imbiribajr/MEU_CONSOLE_FPGA_DE0_SD/fotos/IMG_20260413_175017.jpg

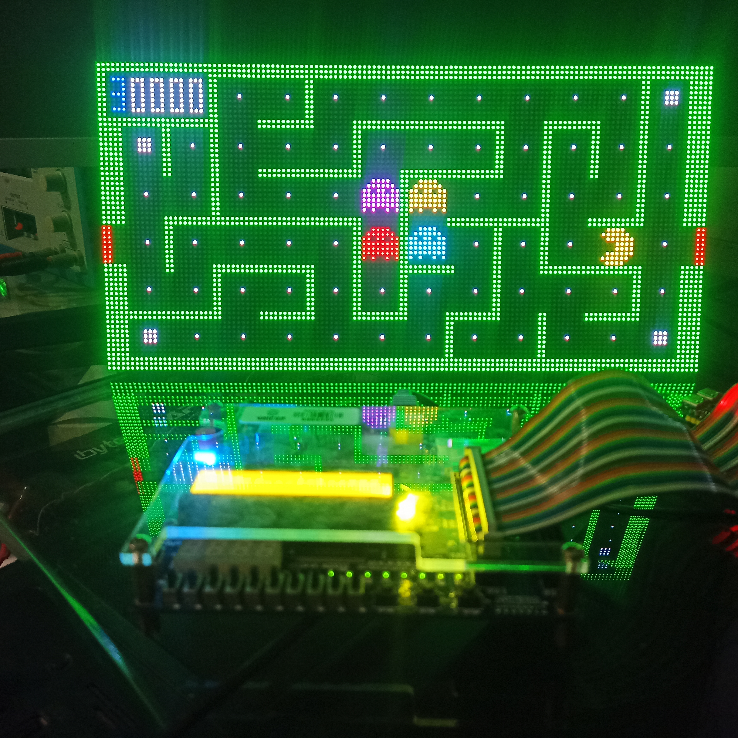
fotos/IMG_20260413_175017.jpg
