imbiribajr/MEU_CONSOLE_FPGA_DE0_SD/fotos/WhatsApp Image 2026-05-14 at 15.44.31 (2).jpeg

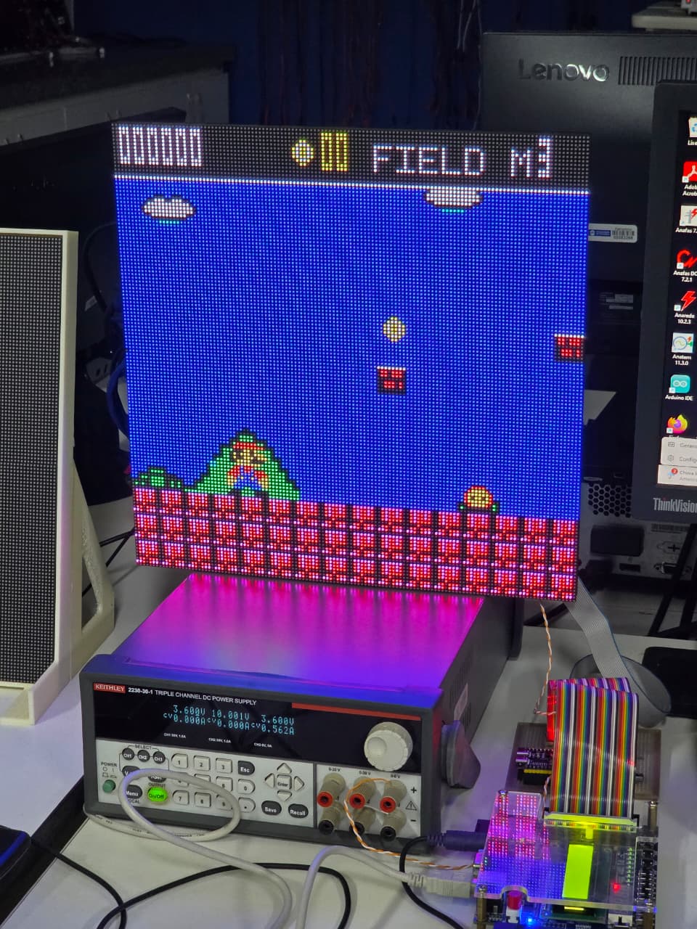
fotos/WhatsApp Image 2026-05-14 at 15.44.31 (2).jpeg
