imbiribajr/MEU_CONSOLE_FPGA_DE0_SD/hardware/NiosII_ps2/synthesis/niosii_ps2_rst_controller.vhd

-- niosii_ps2_rst_controller.vhd

-- Generated using ACDS version 13.0sp1 232 at 2026.03.27.22:52:36

library IEEE;
use IEEE.std_logic_1164.all;
use IEEE.numeric_std.all;

entity niosii_ps2_rst_controller is
	generic (
		NUM_RESET_INPUTS        : integer := 3;
		OUTPUT_RESET_SYNC_EDGES : string  := "deassert";
		SYNC_DEPTH              : integer := 2;
		RESET_REQUEST_PRESENT   : integer := 1
	);
	port (
		reset_in0  : in  std_logic := '0'; -- reset_in0.reset
		reset_in1  : in  std_logic := '0'; -- reset_in1.reset
		reset_in2  : in  std_logic := '0'; -- reset_in2.reset
		clk        : in  std_logic := '0'; --       clk.clk
		reset_out  : out std_logic;        -- reset_out.reset
		reset_req  : out std_logic;        --          .reset_req
		reset_in10 : in  std_logic := '0';
		reset_in11 : in  std_logic := '0';
		reset_in12 : in  std_logic := '0';
		reset_in13 : in  std_logic := '0';
		reset_in14 : in  std_logic := '0';
		reset_in15 : in  std_logic := '0';
		reset_in3  : in  std_logic := '0';
		reset_in4  : in  std_logic := '0';
		reset_in5  : in  std_logic := '0';
		reset_in6  : in  std_logic := '0';
		reset_in7  : in  std_logic := '0';
		reset_in8  : in  std_logic := '0';
		reset_in9  : in  std_logic := '0'
	);
end entity niosii_ps2_rst_controller;

architecture rtl of niosii_ps2_rst_controller is
	component altera_reset_controller is
		generic (
			NUM_RESET_INPUTS        : integer := 6;
			OUTPUT_RESET_SYNC_EDGES : string  := "deassert";
			SYNC_DEPTH              : integer := 2;
			RESET_REQUEST_PRESENT   : integer := 0
		);
		port (
			reset_in0  : in  std_logic := 'X'; -- reset
			reset_in1  : in  std_logic := 'X'; -- reset
			reset_in2  : in  std_logic := 'X'; -- reset
			clk        : in  std_logic := 'X'; -- clk
			reset_out  : out std_logic;        -- reset
			reset_req  : out std_logic;        -- reset_req
			reset_in3  : in  std_logic := 'X'; -- reset
			reset_in4  : in  std_logic := 'X'; -- reset
			reset_in5  : in  std_logic := 'X'; -- reset
			reset_in6  : in  std_logic := 'X'; -- reset
			reset_in7  : in  std_logic := 'X'; -- reset
			reset_in8  : in  std_logic := 'X'; -- reset
			reset_in9  : in  std_logic := 'X'; -- reset
			reset_in10 : in  std_logic := 'X'; -- reset
			reset_in11 : in  std_logic := 'X'; -- reset
			reset_in12 : in  std_logic := 'X'; -- reset
			reset_in13 : in  std_logic := 'X'; -- reset
			reset_in14 : in  std_logic := 'X'; -- reset
			reset_in15 : in  std_logic := 'X'  -- reset
		);
	end component altera_reset_controller;

begin

	rst_controller : component altera_reset_controller
		generic map (
			NUM_RESET_INPUTS        => NUM_RESET_INPUTS,
			OUTPUT_RESET_SYNC_EDGES => OUTPUT_RESET_SYNC_EDGES,
			SYNC_DEPTH              => SYNC_DEPTH,
			RESET_REQUEST_PRESENT   => RESET_REQUEST_PRESENT
		)
		port map (
			reset_in0  => reset_in0, -- reset_in0.reset
			reset_in1  => reset_in1, -- reset_in1.reset
			reset_in2  => reset_in2, -- reset_in2.reset
			clk        => clk,       --       clk.clk
			reset_out  => reset_out, -- reset_out.reset
			reset_req  => reset_req, --          .reset_req
			reset_in3  => '0',       -- (terminated)
			reset_in4  => '0',       -- (terminated)
			reset_in5  => '0',       -- (terminated)
			reset_in6  => '0',       -- (terminated)
			reset_in7  => '0',       -- (terminated)
			reset_in8  => '0',       -- (terminated)
			reset_in9  => '0',       -- (terminated)
			reset_in10 => '0',       -- (terminated)
			reset_in11 => '0',       -- (terminated)
			reset_in12 => '0',       -- (terminated)
			reset_in13 => '0',       -- (terminated)
			reset_in14 => '0',       -- (terminated)
			reset_in15 => '0'        -- (terminated)
		);

end architecture rtl; -- of niosii_ps2_rst_controller
