imbiribajr/MEU_CONSOLE_FPGA_DE0_SD/software/bsp/system.h

/*
 * system.h - SOPC Builder system and BSP software package information
 *
 * Machine generated for CPU 'nios2_qsys_0' in SOPC Builder design 'NiosII_ps2'
 * SOPC Builder design path: F:/Jogos_FPGA/MEU_CONSOLE_FPGA_DE0_SD/hardware/niosII_ps2.sopcinfo
 *
 * Generated: Mon Apr 13 18:09:35 BRT 2026
 */

/*
 * DO NOT MODIFY THIS FILE
 *
 * Changing this file will have subtle consequences
 * which will almost certainly lead to a nonfunctioning
 * system. If you do modify this file, be aware that your
 * changes will be overwritten and lost when this file
 * is generated again.
 *
 * DO NOT MODIFY THIS FILE
 */

/*
 * License Agreement
 *
 * Copyright (c) 2008
 * Altera Corporation, San Jose, California, USA.
 * All rights reserved.
 *
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
 * This agreement shall be governed in all respects by the laws of the State
 * of California and by the laws of the United States of America.
 */

#ifndef __SYSTEM_H_
#define __SYSTEM_H_

/* Include definitions from linker script generator */
#include "linker.h"


/*
 * CPU configuration
 *
 */

#define ALT_CPU_ARCHITECTURE "altera_nios2_qsys"
#define ALT_CPU_BIG_ENDIAN 0
#define ALT_CPU_BREAK_ADDR 0x1810820
#define ALT_CPU_CPU_FREQ 50000000u
#define ALT_CPU_CPU_ID_SIZE 1
#define ALT_CPU_CPU_ID_VALUE 0x00000000
#define ALT_CPU_CPU_IMPLEMENTATION "fast"
#define ALT_CPU_DATA_ADDR_WIDTH 0x19
#define ALT_CPU_DCACHE_LINE_SIZE 32
#define ALT_CPU_DCACHE_LINE_SIZE_LOG2 5
#define ALT_CPU_DCACHE_SIZE 2048
#define ALT_CPU_EXCEPTION_ADDR 0x180c020
#define ALT_CPU_FLUSHDA_SUPPORTED
#define ALT_CPU_FREQ 50000000
#define ALT_CPU_HARDWARE_DIVIDE_PRESENT 1
#define ALT_CPU_HARDWARE_MULTIPLY_PRESENT 1
#define ALT_CPU_HARDWARE_MULX_PRESENT 0
#define ALT_CPU_HAS_DEBUG_CORE 1
#define ALT_CPU_HAS_DEBUG_STUB
#define ALT_CPU_HAS_JMPI_INSTRUCTION
#define ALT_CPU_ICACHE_LINE_SIZE 32
#define ALT_CPU_ICACHE_LINE_SIZE_LOG2 5
#define ALT_CPU_ICACHE_SIZE 4096
#define ALT_CPU_INITDA_SUPPORTED
#define ALT_CPU_INST_ADDR_WIDTH 0x19
#define ALT_CPU_NAME "nios2_qsys_0"
#define ALT_CPU_NUM_OF_SHADOW_REG_SETS 0
#define ALT_CPU_RESET_ADDR 0x180c000


/*
 * CPU configuration (with legacy prefix - don't use these anymore)
 *
 */

#define NIOS2_BIG_ENDIAN 0
#define NIOS2_BREAK_ADDR 0x1810820
#define NIOS2_CPU_FREQ 50000000u
#define NIOS2_CPU_ID_SIZE 1
#define NIOS2_CPU_ID_VALUE 0x00000000
#define NIOS2_CPU_IMPLEMENTATION "fast"
#define NIOS2_DATA_ADDR_WIDTH 0x19
#define NIOS2_DCACHE_LINE_SIZE 32
#define NIOS2_DCACHE_LINE_SIZE_LOG2 5
#define NIOS2_DCACHE_SIZE 2048
#define NIOS2_EXCEPTION_ADDR 0x180c020
#define NIOS2_FLUSHDA_SUPPORTED
#define NIOS2_HARDWARE_DIVIDE_PRESENT 1
#define NIOS2_HARDWARE_MULTIPLY_PRESENT 1
#define NIOS2_HARDWARE_MULX_PRESENT 0
#define NIOS2_HAS_DEBUG_CORE 1
#define NIOS2_HAS_DEBUG_STUB
#define NIOS2_HAS_JMPI_INSTRUCTION
#define NIOS2_ICACHE_LINE_SIZE 32
#define NIOS2_ICACHE_LINE_SIZE_LOG2 5
#define NIOS2_ICACHE_SIZE 4096
#define NIOS2_INITDA_SUPPORTED
#define NIOS2_INST_ADDR_WIDTH 0x19
#define NIOS2_NUM_OF_SHADOW_REG_SETS 0
#define NIOS2_RESET_ADDR 0x180c000


/*
 * Define for each module class mastered by the CPU
 *
 */

#define __ALTERA_AVALON_JTAG_UART
#define __ALTERA_AVALON_NEW_SDRAM_CONTROLLER
#define __ALTERA_AVALON_ONCHIP_MEMORY2
#define __ALTERA_AVALON_PIO
#define __ALTERA_AVALON_SPI
#define __ALTERA_AVALON_SYSID_QSYS
#define __ALTERA_AVALON_UART
#define __ALTERA_GENERIC_TRISTATE_CONTROLLER
#define __ALTERA_NIOS2_QSYS
#define __LED_MATRIX_AVALON
#define __PS2_INTERFACE


/*
 * System configuration
 *
 */

#define ALT_DEVICE_FAMILY "Cyclone III"
#define ALT_ENHANCED_INTERRUPT_API_PRESENT
#define ALT_IRQ_BASE NULL
#define ALT_LOG_PORT "/dev/null"
#define ALT_LOG_PORT_BASE 0x0
#define ALT_LOG_PORT_DEV null
#define ALT_LOG_PORT_TYPE ""
#define ALT_NUM_EXTERNAL_INTERRUPT_CONTROLLERS 0
#define ALT_NUM_INTERNAL_INTERRUPT_CONTROLLERS 1
#define ALT_NUM_INTERRUPT_CONTROLLERS 1
#define ALT_STDERR "/dev/jtag_uart_0"
#define ALT_STDERR_BASE 0x18110b8
#define ALT_STDERR_DEV jtag_uart_0
#define ALT_STDERR_IS_JTAG_UART
#define ALT_STDERR_PRESENT
#define ALT_STDERR_TYPE "altera_avalon_jtag_uart"
#define ALT_STDIN "/dev/jtag_uart_0"
#define ALT_STDIN_BASE 0x18110b8
#define ALT_STDIN_DEV jtag_uart_0
#define ALT_STDIN_IS_JTAG_UART
#define ALT_STDIN_PRESENT
#define ALT_STDIN_TYPE "altera_avalon_jtag_uart"
#define ALT_STDOUT "/dev/jtag_uart_0"
#define ALT_STDOUT_BASE 0x18110b8
#define ALT_STDOUT_DEV jtag_uart_0
#define ALT_STDOUT_IS_JTAG_UART
#define ALT_STDOUT_PRESENT
#define ALT_STDOUT_TYPE "altera_avalon_jtag_uart"
#define ALT_SYSTEM_NAME "NiosII_ps2"


/*
 * generic_tristate_controller_0 configuration
 *
 */

#define ALT_MODULE_CLASS_generic_tristate_controller_0 altera_generic_tristate_controller
#define GENERIC_TRISTATE_CONTROLLER_0_BASE 0x1400000
#define GENERIC_TRISTATE_CONTROLLER_0_HOLD_VALUE 0
#define GENERIC_TRISTATE_CONTROLLER_0_IRQ -1
#define GENERIC_TRISTATE_CONTROLLER_0_IRQ_INTERRUPT_CONTROLLER_ID -1
#define GENERIC_TRISTATE_CONTROLLER_0_NAME "/dev/generic_tristate_controller_0"
#define GENERIC_TRISTATE_CONTROLLER_0_SETUP_VALUE 0
#define GENERIC_TRISTATE_CONTROLLER_0_SIZE 262144u
#define GENERIC_TRISTATE_CONTROLLER_0_SPAN 4194304
#define GENERIC_TRISTATE_CONTROLLER_0_TIMING_UNITS "ns"
#define GENERIC_TRISTATE_CONTROLLER_0_TYPE "altera_generic_tristate_controller"
#define GENERIC_TRISTATE_CONTROLLER_0_WAIT_VALUE 0


/*
 * hal configuration
 *
 */

#define ALT_MAX_FD 4
#define ALT_SYS_CLK none
#define ALT_TIMESTAMP_CLK none


/*
 * i2c_clk configuration
 *
 */

#define ALT_MODULE_CLASS_i2c_clk altera_avalon_pio
#define I2C_CLK_BASE 0x1811080
#define I2C_CLK_BIT_CLEARING_EDGE_REGISTER 0
#define I2C_CLK_BIT_MODIFYING_OUTPUT_REGISTER 0
#define I2C_CLK_CAPTURE 0
#define I2C_CLK_DATA_WIDTH 1
#define I2C_CLK_DO_TEST_BENCH_WIRING 0
#define I2C_CLK_DRIVEN_SIM_VALUE 0
#define I2C_CLK_EDGE_TYPE "NONE"
#define I2C_CLK_FREQ 50000000
#define I2C_CLK_HAS_IN 0
#define I2C_CLK_HAS_OUT 1
#define I2C_CLK_HAS_TRI 0
#define I2C_CLK_IRQ -1
#define I2C_CLK_IRQ_INTERRUPT_CONTROLLER_ID -1
#define I2C_CLK_IRQ_TYPE "NONE"
#define I2C_CLK_NAME "/dev/i2c_clk"
#define I2C_CLK_RESET_VALUE 0
#define I2C_CLK_SPAN 16
#define I2C_CLK_TYPE "altera_avalon_pio"


/*
 * i2c_sda configuration
 *
 */

#define ALT_MODULE_CLASS_i2c_sda altera_avalon_pio
#define I2C_SDA_BASE 0x1811070
#define I2C_SDA_BIT_CLEARING_EDGE_REGISTER 0
#define I2C_SDA_BIT_MODIFYING_OUTPUT_REGISTER 0
#define I2C_SDA_CAPTURE 0
#define I2C_SDA_DATA_WIDTH 1
#define I2C_SDA_DO_TEST_BENCH_WIRING 0
#define I2C_SDA_DRIVEN_SIM_VALUE 0
#define I2C_SDA_EDGE_TYPE "NONE"
#define I2C_SDA_FREQ 50000000
#define I2C_SDA_HAS_IN 0
#define I2C_SDA_HAS_OUT 0
#define I2C_SDA_HAS_TRI 1
#define I2C_SDA_IRQ -1
#define I2C_SDA_IRQ_INTERRUPT_CONTROLLER_ID -1
#define I2C_SDA_IRQ_TYPE "NONE"
#define I2C_SDA_NAME "/dev/i2c_sda"
#define I2C_SDA_RESET_VALUE 0
#define I2C_SDA_SPAN 16
#define I2C_SDA_TYPE "altera_avalon_pio"


/*
 * jtag_uart_0 configuration
 *
 */

#define ALT_MODULE_CLASS_jtag_uart_0 altera_avalon_jtag_uart
#define JTAG_UART_0_BASE 0x18110b8
#define JTAG_UART_0_IRQ 0
#define JTAG_UART_0_IRQ_INTERRUPT_CONTROLLER_ID 0
#define JTAG_UART_0_NAME "/dev/jtag_uart_0"
#define JTAG_UART_0_READ_DEPTH 64
#define JTAG_UART_0_READ_THRESHOLD 8
#define JTAG_UART_0_SPAN 8
#define JTAG_UART_0_TYPE "altera_avalon_jtag_uart"
#define JTAG_UART_0_WRITE_DEPTH 64
#define JTAG_UART_0_WRITE_THRESHOLD 8


/*
 * led_matrix_avalon_0 configuration
 *
 */

#define ALT_MODULE_CLASS_led_matrix_avalon_0 led_matrix_avalon
#define LED_MATRIX_AVALON_0_BASE 0x1808000
#define LED_MATRIX_AVALON_0_IRQ -1
#define LED_MATRIX_AVALON_0_IRQ_INTERRUPT_CONTROLLER_ID -1
#define LED_MATRIX_AVALON_0_NAME "/dev/led_matrix_avalon_0"
#define LED_MATRIX_AVALON_0_SPAN 16384
#define LED_MATRIX_AVALON_0_TYPE "led_matrix_avalon"


/*
 * new_sdram_controller_0 configuration
 *
 */

#define ALT_MODULE_CLASS_new_sdram_controller_0 altera_avalon_new_sdram_controller
#define NEW_SDRAM_CONTROLLER_0_BASE 0x800000
#define NEW_SDRAM_CONTROLLER_0_CAS_LATENCY 3
#define NEW_SDRAM_CONTROLLER_0_CONTENTS_INFO
#define NEW_SDRAM_CONTROLLER_0_INIT_NOP_DELAY 0.0
#define NEW_SDRAM_CONTROLLER_0_INIT_REFRESH_COMMANDS 2
#define NEW_SDRAM_CONTROLLER_0_IRQ -1
#define NEW_SDRAM_CONTROLLER_0_IRQ_INTERRUPT_CONTROLLER_ID -1
#define NEW_SDRAM_CONTROLLER_0_IS_INITIALIZED 1
#define NEW_SDRAM_CONTROLLER_0_NAME "/dev/new_sdram_controller_0"
#define NEW_SDRAM_CONTROLLER_0_POWERUP_DELAY 100.0
#define NEW_SDRAM_CONTROLLER_0_REFRESH_PERIOD 7.8125
#define NEW_SDRAM_CONTROLLER_0_REGISTER_DATA_IN 1
#define NEW_SDRAM_CONTROLLER_0_SDRAM_ADDR_WIDTH 0x16
#define NEW_SDRAM_CONTROLLER_0_SDRAM_BANK_WIDTH 2
#define NEW_SDRAM_CONTROLLER_0_SDRAM_COL_WIDTH 8
#define NEW_SDRAM_CONTROLLER_0_SDRAM_DATA_WIDTH 16
#define NEW_SDRAM_CONTROLLER_0_SDRAM_NUM_BANKS 4
#define NEW_SDRAM_CONTROLLER_0_SDRAM_NUM_CHIPSELECTS 1
#define NEW_SDRAM_CONTROLLER_0_SDRAM_ROW_WIDTH 12
#define NEW_SDRAM_CONTROLLER_0_SHARED_DATA 0
#define NEW_SDRAM_CONTROLLER_0_SIM_MODEL_BASE 0
#define NEW_SDRAM_CONTROLLER_0_SPAN 8388608
#define NEW_SDRAM_CONTROLLER_0_STARVATION_INDICATOR 0
#define NEW_SDRAM_CONTROLLER_0_TRISTATE_BRIDGE_SLAVE ""
#define NEW_SDRAM_CONTROLLER_0_TYPE "altera_avalon_new_sdram_controller"
#define NEW_SDRAM_CONTROLLER_0_T_AC 5.5
#define NEW_SDRAM_CONTROLLER_0_T_MRD 3
#define NEW_SDRAM_CONTROLLER_0_T_RCD 20.0
#define NEW_SDRAM_CONTROLLER_0_T_RFC 70.0
#define NEW_SDRAM_CONTROLLER_0_T_RP 20.0
#define NEW_SDRAM_CONTROLLER_0_T_WR 14.0


/*
 * onchip_memory2_0 configuration
 *
 */

#define ALT_MODULE_CLASS_onchip_memory2_0 altera_avalon_onchip_memory2
#define ONCHIP_MEMORY2_0_ALLOW_IN_SYSTEM_MEMORY_CONTENT_EDITOR 0
#define ONCHIP_MEMORY2_0_ALLOW_MRAM_SIM_CONTENTS_ONLY_FILE 0
#define ONCHIP_MEMORY2_0_BASE 0x180c000
#define ONCHIP_MEMORY2_0_CONTENTS_INFO ""
#define ONCHIP_MEMORY2_0_DUAL_PORT 0
#define ONCHIP_MEMORY2_0_GUI_RAM_BLOCK_TYPE "AUTO"
#define ONCHIP_MEMORY2_0_INIT_CONTENTS_FILE "NiosII_ps2_onchip_memory2_0"
#define ONCHIP_MEMORY2_0_INIT_MEM_CONTENT 1
#define ONCHIP_MEMORY2_0_INSTANCE_ID "NONE"
#define ONCHIP_MEMORY2_0_IRQ -1
#define ONCHIP_MEMORY2_0_IRQ_INTERRUPT_CONTROLLER_ID -1
#define ONCHIP_MEMORY2_0_NAME "/dev/onchip_memory2_0"
#define ONCHIP_MEMORY2_0_NON_DEFAULT_INIT_FILE_ENABLED 0
#define ONCHIP_MEMORY2_0_RAM_BLOCK_TYPE "AUTO"
#define ONCHIP_MEMORY2_0_READ_DURING_WRITE_MODE "DONT_CARE"
#define ONCHIP_MEMORY2_0_SINGLE_CLOCK_OP 0
#define ONCHIP_MEMORY2_0_SIZE_MULTIPLE 1
#define ONCHIP_MEMORY2_0_SIZE_VALUE 16384
#define ONCHIP_MEMORY2_0_SPAN 16384
#define ONCHIP_MEMORY2_0_TYPE "altera_avalon_onchip_memory2"
#define ONCHIP_MEMORY2_0_WRITABLE 1


/*
 * pio_0 configuration
 *
 */

#define ALT_MODULE_CLASS_pio_0 altera_avalon_pio
#define PIO_0_BASE 0x1811090
#define PIO_0_BIT_CLEARING_EDGE_REGISTER 0
#define PIO_0_BIT_MODIFYING_OUTPUT_REGISTER 0
#define PIO_0_CAPTURE 0
#define PIO_0_DATA_WIDTH 4
#define PIO_0_DO_TEST_BENCH_WIRING 0
#define PIO_0_DRIVEN_SIM_VALUE 0
#define PIO_0_EDGE_TYPE "NONE"
#define PIO_0_FREQ 50000000
#define PIO_0_HAS_IN 1
#define PIO_0_HAS_OUT 0
#define PIO_0_HAS_TRI 0
#define PIO_0_IRQ -1
#define PIO_0_IRQ_INTERRUPT_CONTROLLER_ID -1
#define PIO_0_IRQ_TYPE "NONE"
#define PIO_0_NAME "/dev/pio_0"
#define PIO_0_RESET_VALUE 0
#define PIO_0_SPAN 16
#define PIO_0_TYPE "altera_avalon_pio"


/*
 * ps2_interface_0 configuration
 *
 */

#define ALT_MODULE_CLASS_ps2_interface_0 ps2_interface
#define PS2_INTERFACE_0_BASE 0x18110c4
#define PS2_INTERFACE_0_IRQ -1
#define PS2_INTERFACE_0_IRQ_INTERRUPT_CONTROLLER_ID -1
#define PS2_INTERFACE_0_NAME "/dev/ps2_interface_0"
#define PS2_INTERFACE_0_SPAN 4
#define PS2_INTERFACE_0_TYPE "ps2_interface"


/*
 * sd_spi_0 configuration
 *
 */

#define ALT_MODULE_CLASS_sd_spi_0 altera_avalon_spi
#define SD_SPI_0_BASE 0x1811000
#define SD_SPI_0_CLOCKMULT 1
#define SD_SPI_0_CLOCKPHASE 0
#define SD_SPI_0_CLOCKPOLARITY 0
#define SD_SPI_0_CLOCKUNITS "Hz"
#define SD_SPI_0_DATABITS 8
#define SD_SPI_0_DATAWIDTH 16
#define SD_SPI_0_DELAYMULT "1.0E-9"
#define SD_SPI_0_DELAYUNITS "ns"
#define SD_SPI_0_EXTRADELAY 0
#define SD_SPI_0_INSERT_SYNC 0
#define SD_SPI_0_IRQ 2
#define SD_SPI_0_IRQ_INTERRUPT_CONTROLLER_ID 0
#define SD_SPI_0_ISMASTER 1
#define SD_SPI_0_LSBFIRST 0
#define SD_SPI_0_NAME "/dev/sd_spi_0"
#define SD_SPI_0_NUMSLAVES 1
#define SD_SPI_0_PREFIX "spi_"
#define SD_SPI_0_SPAN 32
#define SD_SPI_0_SYNC_REG_DEPTH 2
#define SD_SPI_0_TARGETCLOCK 128000u
#define SD_SPI_0_TARGETSSDELAY "0.0"
#define SD_SPI_0_TYPE "altera_avalon_spi"


/*
 * sysid_qsys_0 configuration
 *
 */

#define ALT_MODULE_CLASS_sysid_qsys_0 altera_avalon_sysid_qsys
#define SYSID_QSYS_0_BASE 0x18110b0
#define SYSID_QSYS_0_ID 0
#define SYSID_QSYS_0_IRQ -1
#define SYSID_QSYS_0_IRQ_INTERRUPT_CONTROLLER_ID -1
#define SYSID_QSYS_0_NAME "/dev/sysid_qsys_0"
#define SYSID_QSYS_0_SPAN 8
#define SYSID_QSYS_0_TIMESTAMP 1776110056
#define SYSID_QSYS_0_TYPE "altera_avalon_sysid_qsys"


/*
 * uart_0 configuration
 *
 */

#define ALT_MODULE_CLASS_uart_0 altera_avalon_uart
#define UART_0_BASE 0x1811020
#define UART_0_BAUD 9600
#define UART_0_DATA_BITS 8
#define UART_0_FIXED_BAUD 1
#define UART_0_FREQ 50000000
#define UART_0_IRQ 1
#define UART_0_IRQ_INTERRUPT_CONTROLLER_ID 0
#define UART_0_NAME "/dev/uart_0"
#define UART_0_PARITY 'N'
#define UART_0_SIM_CHAR_STREAM ""
#define UART_0_SIM_TRUE_BAUD 0
#define UART_0_SPAN 32
#define UART_0_STOP_BITS 1
#define UART_0_SYNC_REG_DEPTH 2
#define UART_0_TYPE "altera_avalon_uart"
#define UART_0_USE_CTS_RTS 0
#define UART_0_USE_EOP_REGISTER 0

#endif /* __SYSTEM_H_ */
