imbiribajr/MEU_CONSOLE_FPGA_DE0_SD/hardware/NiosII_ps2/synthesis/submodules/NiosII_ps2_addr_router.sv

// (C) 2001-2013 Altera Corporation. All rights reserved.
// Your use of Altera Corporation's design tools, logic functions and other 
// software and tools, and its AMPP partner logic functions, and any output 
// files any of the foregoing (including device programming or simulation 
// files), and any associated documentation or information are expressly subject 
// to the terms and conditions of the Altera Program License Subscription 
// Agreement, Altera MegaCore Function License Agreement, or other applicable 
// license agreement, including, without limitation, that your use is for the 
// sole purpose of programming logic devices manufactured by Altera and sold by 
// Altera or its authorized distributors.  Please refer to the applicable 
// agreement for further details.


// (C) 2001-2013 Altera Corporation. All rights reserved.
// Your use of Altera Corporation's design tools, logic functions and other 
// software and tools, and its AMPP partner logic functions, and any output 
// files any of the foregoing (including device programming or simulation 
// files), and any associated documentation or information are expressly subject 
// to the terms and conditions of the Altera Program License Subscription 
// Agreement, Altera MegaCore Function License Agreement, or other applicable 
// license agreement, including, without limitation, that your use is for the 
// sole purpose of programming logic devices manufactured by Altera and sold by 
// Altera or its authorized distributors.  Please refer to the applicable 
// agreement for further details.


// $Id: //acds/rel/13.0sp1/ip/merlin/altera_merlin_router/altera_merlin_router.sv.terp#1 $
// $Revision: #1 $
// $Date: 2013/03/07 $
// $Author: swbranch $

// -------------------------------------------------------
// Merlin Router
//
// Asserts the appropriate one-hot encoded channel based on 
// either (a) the address or (b) the dest id. The DECODER_TYPE
// parameter controls this behaviour. 0 means address decoder,
// 1 means dest id decoder.
//
// In the case of (a), it also sets the destination id.
// -------------------------------------------------------

`timescale 1 ns / 1 ns

module NiosII_ps2_addr_router_default_decode
  #(
     parameter DEFAULT_CHANNEL = 6,
               DEFAULT_WR_CHANNEL = -1,
               DEFAULT_RD_CHANNEL = -1,
               DEFAULT_DESTID = 5 
   )
  (output [89 - 86 : 0] default_destination_id,
   output [13-1 : 0] default_wr_channel,
   output [13-1 : 0] default_rd_channel,
   output [13-1 : 0] default_src_channel
  );

  assign default_destination_id = 
    DEFAULT_DESTID[89 - 86 : 0];

  generate begin : default_decode
    if (DEFAULT_CHANNEL == -1) begin
      assign default_src_channel = '0;
    end
    else begin
      assign default_src_channel = 13'b1 << DEFAULT_CHANNEL;
    end
  end
  endgenerate

  generate begin : default_decode_rw
    if (DEFAULT_RD_CHANNEL == -1) begin
      assign default_wr_channel = '0;
      assign default_rd_channel = '0;
    end
    else begin
      assign default_wr_channel = 13'b1 << DEFAULT_WR_CHANNEL;
      assign default_rd_channel = 13'b1 << DEFAULT_RD_CHANNEL;
    end
  end
  endgenerate

endmodule


module NiosII_ps2_addr_router
(
    // -------------------
    // Clock & Reset
    // -------------------
    input clk,
    input reset,

    // -------------------
    // Command Sink (Input)
    // -------------------
    input                       sink_valid,
    input  [100-1 : 0]    sink_data,
    input                       sink_startofpacket,
    input                       sink_endofpacket,
    output                      sink_ready,

    // -------------------
    // Command Source (Output)
    // -------------------
    output                          src_valid,
    output reg [100-1    : 0] src_data,
    output reg [13-1 : 0] src_channel,
    output                          src_startofpacket,
    output                          src_endofpacket,
    input                           src_ready
);

    // -------------------------------------------------------
    // Local parameters and variables
    // -------------------------------------------------------
    localparam PKT_ADDR_H = 60;
    localparam PKT_ADDR_L = 36;
    localparam PKT_DEST_ID_H = 89;
    localparam PKT_DEST_ID_L = 86;
    localparam PKT_PROTECTION_H = 93;
    localparam PKT_PROTECTION_L = 91;
    localparam ST_DATA_W = 100;
    localparam ST_CHANNEL_W = 13;
    localparam DECODER_TYPE = 0;

    localparam PKT_TRANS_WRITE = 63;
    localparam PKT_TRANS_READ  = 64;

    localparam PKT_ADDR_W = PKT_ADDR_H-PKT_ADDR_L + 1;
    localparam PKT_DEST_ID_W = PKT_DEST_ID_H-PKT_DEST_ID_L + 1;



    // -------------------------------------------------------
    // Figure out the number of bits to mask off for each slave span
    // during address decoding
    // -------------------------------------------------------
    localparam PAD0 = log2ceil(64'h1000000 - 64'h800000); 
    localparam PAD1 = log2ceil(64'h1800000 - 64'h1400000); 
    localparam PAD2 = log2ceil(64'h180c000 - 64'h1808000); 
    localparam PAD3 = log2ceil(64'h1810000 - 64'h180c000); 
    localparam PAD4 = log2ceil(64'h1811000 - 64'h1810800); 
    localparam PAD5 = log2ceil(64'h1811080 - 64'h1811070); 
    localparam PAD6 = log2ceil(64'h1811090 - 64'h1811080); 
    localparam PAD7 = log2ceil(64'h18110a0 - 64'h1811090); 
    localparam PAD8 = log2ceil(64'h18110b8 - 64'h18110b0); 
    localparam PAD9 = log2ceil(64'h18110c0 - 64'h18110b8); 
    localparam PAD10 = log2ceil(64'h18110c8 - 64'h18110c4); 
    // -------------------------------------------------------
    // Work out which address bits are significant based on the
    // address range of the slaves. If the required width is too
    // large or too small, we use the address field width instead.
    // -------------------------------------------------------
    localparam ADDR_RANGE = 64'h18110c8;
    localparam RANGE_ADDR_WIDTH = log2ceil(ADDR_RANGE);
    localparam OPTIMIZED_ADDR_H = (RANGE_ADDR_WIDTH > PKT_ADDR_W) ||
                                  (RANGE_ADDR_WIDTH == 0) ?
                                        PKT_ADDR_H :
                                        PKT_ADDR_L + RANGE_ADDR_WIDTH - 1;

    localparam RG = RANGE_ADDR_WIDTH-1;

      wire [PKT_ADDR_W-1 : 0] address = sink_data[OPTIMIZED_ADDR_H : PKT_ADDR_L];

    // -------------------------------------------------------
    // Pass almost everything through, untouched
    // -------------------------------------------------------
    assign sink_ready        = src_ready;
    assign src_valid         = sink_valid;
    assign src_startofpacket = sink_startofpacket;
    assign src_endofpacket   = sink_endofpacket;

    wire [PKT_DEST_ID_W-1:0] default_destid;
    wire [13-1 : 0] default_src_channel;





    NiosII_ps2_addr_router_default_decode the_default_decode(
      .default_destination_id (default_destid),
      .default_wr_channel   (),
      .default_rd_channel   (),
      .default_src_channel  (default_src_channel)
    );

    always @* begin
        src_data    = sink_data;
        src_channel = default_src_channel;
        src_data[PKT_DEST_ID_H:PKT_DEST_ID_L] = default_destid;

        // --------------------------------------------------
        // Address Decoder
        // Sets the channel and destination ID based on the address
        // --------------------------------------------------

    // ( 0x800000 .. 0x1000000 )
    if ( {address[RG:PAD0],{PAD0{1'b0}}} == 25'h800000   ) begin
            src_channel = 13'b00001000000;
            src_data[PKT_DEST_ID_H:PKT_DEST_ID_L] = 5;
    end

    // ( 0x1400000 .. 0x1800000 )
    if ( {address[RG:PAD1],{PAD1{1'b0}}} == 25'h1400000   ) begin
            src_channel = 13'b10000000000;
            src_data[PKT_DEST_ID_H:PKT_DEST_ID_L] = 0;
    end

    // ( 0x1808000 .. 0x180c000 )
    if ( {address[RG:PAD2],{PAD2{1'b0}}} == 25'h1808000   ) begin
            src_channel = 13'b00000010000;
            src_data[PKT_DEST_ID_H:PKT_DEST_ID_L] = 4;
    end

    // ( 0x180c000 .. 0x1810000 )
    if ( {address[RG:PAD3],{PAD3{1'b0}}} == 25'h180c000   ) begin
            src_channel = 13'b00000000010;
            src_data[PKT_DEST_ID_H:PKT_DEST_ID_L] = 7;
    end

    // ( 0x1810800 .. 0x1811000 )
    if ( {address[RG:PAD4],{PAD4{1'b0}}} == 25'h1810800   ) begin
            src_channel = 13'b00000000001;
            src_data[PKT_DEST_ID_H:PKT_DEST_ID_L] = 6;
    end

    // ( 0x1811070 .. 0x1811080 )
    if ( {address[RG:PAD5],{PAD5{1'b0}}} == 25'h1811070   ) begin
            src_channel = 13'b01000000000;
            src_data[PKT_DEST_ID_H:PKT_DEST_ID_L] = 2;
    end

    // ( 0x1811080 .. 0x1811090 )
    if ( {address[RG:PAD6],{PAD6{1'b0}}} == 25'h1811080   ) begin
            src_channel = 13'b00100000000;
            src_data[PKT_DEST_ID_H:PKT_DEST_ID_L] = 1;
    end

    // ( 0x1811090 .. 0x18110a0 )
    if ( {address[RG:PAD7],{PAD7{1'b0}}} == 25'h1811090   ) begin
            src_channel = 13'b00000001000;
            src_data[PKT_DEST_ID_H:PKT_DEST_ID_L] = 8;
    end

    // ( 0x18110b0 .. 0x18110b8 )
    if ( {address[RG:PAD8],{PAD8{1'b0}}} == 25'h18110b0   ) begin
            src_channel = 13'b00000100000;
            src_data[PKT_DEST_ID_H:PKT_DEST_ID_L] = 11;
    end

    // ( 0x18110b8 .. 0x18110c0 )
    if ( {address[RG:PAD9],{PAD9{1'b0}}} == 25'h18110b8   ) begin
            src_channel = 13'b00000000100;
            src_data[PKT_DEST_ID_H:PKT_DEST_ID_L] = 3;
    end

    // ( 0x18110c4 .. 0x18110c8 )
    if ( {address[RG:PAD10],{PAD10{1'b0}}} == 25'h18110c4   ) begin
            src_channel = 13'b00010000000;
            src_data[PKT_DEST_ID_H:PKT_DEST_ID_L] = 9;
    end

end


    // --------------------------------------------------
    // Ceil(log2()) function
    // --------------------------------------------------
    function integer log2ceil;
        input reg[65:0] val;
        reg [65:0] i;

        begin
            i = 1;
            log2ceil = 0;

            while (i < val) begin
                log2ceil = log2ceil + 1;
                i = i << 1;
            end
        end
    endfunction

endmodule
