imbiribajr/MEU_CONSOLE_FPGA_DE0_SD/hardware/NiosII_ps2/synthesis/submodules/niosII_ps2_sd_spi_0.v

//Legal Notice: (C)2026 Altera Corporation. All rights reserved.  Your
//use of Altera Corporation's design tools, logic functions and other
//software and tools, and its AMPP partner logic functions, and any
//output files any of the foregoing (including device programming or
//simulation files), and any associated documentation or information are
//expressly subject to the terms and conditions of the Altera Program
//License Subscription Agreement or other applicable license agreement,
//including, without limitation, that your use is for the sole purpose
//of programming logic devices manufactured by Altera and sold by Altera
//or its authorized distributors.  Please refer to the applicable
//agreement for further details.

// synthesis translate_off
`timescale 1ns / 1ps
// synthesis translate_on

// turn off superfluous verilog processor warnings 
// altera message_level Level1 
// altera message_off 10034 10035 10036 10037 10230 10240 10030 

//Register map:
//addr      register      type
//0         read data     r
//1         write data    w
//2         status        r/w
//3         control       r/w
//4         reserved
//5         slave-enable  r/w
//6         end-of-packet-value r/w
//INPUT_CLOCK: 50000000
//ISMASTER: 1
//DATABITS: 8
//TARGETCLOCK: 128000
//NUMSLAVES: 1
//CPOL: 0
//CPHA: 0
//LSBFIRST: 0
//EXTRADELAY: 0
//TARGETSSDELAY: 0

module NiosII_ps2_sd_spi_0 (
                             // inputs:
                              MISO,
                              clk,
                              data_from_cpu,
                              mem_addr,
                              read_n,
                              reset_n,
                              spi_select,
                              write_n,

                             // outputs:
                              MOSI,
                              SCLK,
                              SS_n,
                              data_to_cpu,
                              dataavailable,
                              endofpacket,
                              irq,
                              readyfordata
                           )
;

  output           MOSI;
  output           SCLK;
  output           SS_n;
  output  [ 15: 0] data_to_cpu;
  output           dataavailable;
  output           endofpacket;
  output           irq;
  output           readyfordata;
  input            MISO;
  input            clk;
  input   [ 15: 0] data_from_cpu;
  input   [  2: 0] mem_addr;
  input            read_n;
  input            reset_n;
  input            spi_select;
  input            write_n;

  wire             E;
  reg              EOP;
  reg              MISO_reg;
  wire             MOSI;
  reg              ROE;
  reg              RRDY;
  wire             SCLK;
  reg              SCLK_reg;
  reg              SSO_reg;
  wire             SS_n;
  wire             TMT;
  reg              TOE;
  wire             TRDY;
  wire             control_wr_strobe;
  reg              data_rd_strobe;
  reg     [ 15: 0] data_to_cpu;
  reg              data_wr_strobe;
  wire             dataavailable;
  wire             ds_MISO;
  wire             enableSS;
  wire             endofpacket;
  reg     [ 15: 0] endofpacketvalue_reg;
  wire             endofpacketvalue_wr_strobe;
  reg              iEOP_reg;
  reg              iE_reg;
  reg              iROE_reg;
  reg              iRRDY_reg;
  reg              iTMT_reg;
  reg              iTOE_reg;
  reg              iTRDY_reg;
  wire             irq;
  reg              irq_reg;
  wire             p1_data_rd_strobe;
  wire    [ 15: 0] p1_data_to_cpu;
  wire             p1_data_wr_strobe;
  wire             p1_rd_strobe;
  wire    [  7: 0] p1_slowcount;
  wire             p1_wr_strobe;
  reg              rd_strobe;
  wire             readyfordata;
  reg     [  7: 0] rx_holding_reg;
  reg     [  7: 0] shift_reg;
  wire             slaveselect_wr_strobe;
  wire             slowclock;
  reg     [  7: 0] slowcount;
  wire    [ 10: 0] spi_control;
  reg     [ 15: 0] spi_slave_select_holding_reg;
  reg     [ 15: 0] spi_slave_select_reg;
  wire    [ 10: 0] spi_status;
  reg     [  4: 0] state;
  reg              stateZero;
  wire             status_wr_strobe;
  reg              transmitting;
  reg              tx_holding_primed;
  reg     [  7: 0] tx_holding_reg;
  reg              wr_strobe;
  wire             write_shift_reg;
  wire             write_tx_holding;
  //spi_control_port, which is an e_avalon_slave
  assign p1_rd_strobe = ~rd_strobe & spi_select & ~read_n;
  // Read is a two-cycle event.
  always @(posedge clk or negedge reset_n)
    begin
      if (reset_n == 0)
          rd_strobe <= 0;
      else 
        rd_strobe <= p1_rd_strobe;
    end


  assign p1_data_rd_strobe = p1_rd_strobe & (mem_addr == 0);
  always @(posedge clk or negedge reset_n)
    begin
      if (reset_n == 0)
          data_rd_strobe <= 0;
      else 
        data_rd_strobe <= p1_data_rd_strobe;
    end


  assign p1_wr_strobe = ~wr_strobe & spi_select & ~write_n;
  // Write is a two-cycle event.
  always @(posedge clk or negedge reset_n)
    begin
      if (reset_n == 0)
          wr_strobe <= 0;
      else 
        wr_strobe <= p1_wr_strobe;
    end
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
